alexisvl/os2/sims/analog_line_txrx/analog_line_txrx.asc

C1: cap; 33p
I1: load2; PULSE(0 990u 0 10n 10n 1u 2u); load
Q1: npn; 2N3904
Q2: npn; 2N3904
Q3: npn; 2N3904
Q4: npn; 2N3904
R1: res; 150
R2: res; 1k
R3: res; 1k
R4: res; 1k6
R5: res; 75
R6: res; 75
R7: res; 1k6
R8: res; 6k2
R9: res; 75
R10: res; 3k
R11: res; 75
R12: res; 1k2
R13: res; 100
R14: res; 1k2
U1: NE5532
U2: NE5532
V1: voltage; 15
V2: voltage; -15
V3: voltage; 9
V4: voltage; 5
Named nets: 0, V+, V-, +5
.tran 10u
