alexisvl/os2/sims/gfx_digital/gfx_digital.asc

B1: bv; V=(V(hdot0)+2*V(hdot1)+4*V(hdot2))/5
B2: bv; V=(V(posreq0)+2*V(posreq1)+4*V(posreq2))/5
B3: bv; V=(V(pos0)+2*V(pos1)+4*V(pos2))/5
B4: bv; V=(V(field0)+2*V(field1)+4*V(field2))/5
B5: bv; V=(V(fieldreq0)+2*V(fieldreq1)+4*V(fieldreq2))/5
C1: cap; 100p
C2: cap; 100p
C3: cap; 10p
D1: diode; 1N4148
R1: res; 22k
R2: res; 62k
R3: res; 33k
U1: 74hc109; VCC=5  SPEED=1.0  TRIPDT=1e-9 TD=44n
U2: 74hc14
U3: 74hc14
U4: 74hc109; VCC=5  SPEED=1.0  TRIPDT=1e-9 TD=44n
U5: 74hc161
U7: 74hc02
U8: 74hc109; VCC=5  SPEED=1.0  TRIPDT=1e-9 TD=44n
U9: 74hc109; VCC=5  SPEED=1.0  TRIPDT=1e-9 TD=44n
U10: 74hc27
U11: 74hc109; VCC=5  SPEED=1.0  TRIPDT=1e-9 TD=44n
U12: 74hc02
U13: 74hc02
U14: 74hc161
U15: 74hc02
U16: 74hc10
U17: 74hc161
U18: 74hc02
U19: 74hc273; VCC=5  SPEED=1.0  TRIPDT=1e-9 TD=45n
U20: 74hc273; VCC=5  SPEED=1.0  TRIPDT=1e-9 TD=45n
U21: 74hc00
U22: 74hc161
U23: 74hc02
U24: 74hc10
U25: 74hc02
U26: 74hc02
U27: 74hc14
U28: 74hc02
U29: 74hc00
U30: 74hc109; VCC=5  SPEED=1.0  TRIPDT=1e-9 TD=44n
U31: 74hc00
U35: 74hc10
U36: 74hc02
V1: voltage; 5
V2: voltage; 9
V3: voltage; -9
V4: voltage; PULSE(0 5 0 {tr} {tr} {0.5/freq-tr} {1/freq})
V5: voltage; PULSE(0 5 100u 50n 50n 100u)
Named nets: 0, V+, +9, -9, clock, _por, por, hdot0, hdot1, hdot2, DISP, v+, predone, preblank, posclk, posreq0, posreq1, posreq2, pos0, pos1, pos2, charrsp0, charrsp1, charrsp2, charrsp3, charrsp4, charrsp5, brightenrsp, dimrsp, char0, char1, char2, char3, char4, char5, brighten, dim, interfield_blank, hdot, posreq, pos, fieldreq0, fieldreq1, fieldreq2, field0, field1, field2, line2, line1, line0, pix_blank, _rst, _DISP_SYNC, field, fieldreq, nextline, DONE, _blank, donereq, blankout, DISP_SYNC, rst
.param tr 25n
.param freq 1Meg
.tran 20m uic
dot = 5µA
char width = 6; char = 30µA
8 chars per cell, cell = 240µA
inter-cell space: 3 chars or 90µA
cell with space: 330µA
 
CELL0   CELL1   CELL2   CELL3
0µA     330µA   660µA   990µA
 
0µA  240µA480µA         900µA
CELL4CELL5CELL6         CELL7
Character encoding notes:
Characters are 5 pix wide, but encoded at 6. The 6th should be
the inter-character space, and should come FIRST (as the
inter-field blanking eats into it)
Sync DISP to clock
Sync DISP to first dot, stretch DONE at least one entire cycle
DOT COUNTER
counts 0 through 5
POS COUNTER
counts 0 through 8
SYSTEM
BUS
FONT
ROM
Deassert at approx 90°+clk
